lelewel4/Vest-Indicator-bachelor-thesis/Code/Steering wheel - TX/Core/Inc/ADC_functions.h

/*
 * ADC_functions.h
 *
 *  Created on: 12 gru 2022
 *      Author: Jakub Górnisiewicz
 */

#ifndef INC_OTHER_FUNCTIONS_H_
#define INC_OTHER_FUNCTIONS_H_


/*/////////////////////////////////////////////////////////////////////////////
 	 	 	 	 	 	 	 	 DEFINE
*//////////////////////////////////////////////////////////////////////////////

#define DEBUG_PRINTF
//define of the time of high-state diodes to show battery voltage
#define DIODES_ADC_TIME 500


/*/////////////////////////////////////////////////////////////////////////////
 	 	 	 	 	 	 	 	 INCLUDES
*//////////////////////////////////////////////////////////////////////////////


#include "main.h"


/*/////////////////////////////////////////////////////////////////////////////
 	 	 	 	 	 	 	 	 VARIABLES
*//////////////////////////////////////////////////////////////////////////////


//variable for ADC, measurement of battery voltage
extern uint32_t adc_value;


/*/////////////////////////////////////////////////////////////////////////////
 	 	 	 	 	 	 	 	 FUNCTIONS
*//////////////////////////////////////////////////////////////////////////////

uint32_t get_adc_battery_value(void);
void battery_level_show(uint32_t value);


#endif /* INC_OTHER_FUNCTIONS_H_ */
