lelewel4/Vest-Indicator-bachelor-thesis/Code/Steering wheel - TX/Core/Inc/nRF24.h

/*
 * nRF24.h
 *
 *  Created on: 16 paź 2022
 *      Author: Jakub Górnisiewicz
 */

#ifndef INC_NRF24_NRF24_H_
#define INC_NRF24_NRF24_H_


/*/////////////////////////////////////////////////////////////////////////////
 	 	 	 	 	 	 	 	 INCLUDES
*//////////////////////////////////////////////////////////////////////////////


#include "main.h"


/*/////////////////////////////////////////////////////////////////////////////
 	 	 	 	 	 	 	 	 VARIABLES
*//////////////////////////////////////////////////////////////////////////////


extern volatile uint8_t nrf24_rx_flag, nrf24_tx_flag, nrf24_mr_flag;


/*/////////////////////////////////////////////////////////////////////////////
 	 	 	 	 	 	 	 	 FUNCTIONS
*//////////////////////////////////////////////////////////////////////////////


void nRF24_Init(SPI_HandleTypeDef *hspi);


// READ/WRITE REGISTERS
uint8_t nRF24_ReadConfig(void);
void nRF24_WriteConfig(uint8_t conf);
uint8_t nRF24_ReadStatus();
void nRF24_WriteStatus(uint8_t st);

// SWITCHING BETWEEN RX AND TX
void nRF24_RX_Mode(void);
void nRF24_TX_Mode(void);

// RADIO SETTINGS
void nRF24_SetPALevel(uint8_t lev);
void nRF24_SetDataRate(uint8_t dr);
void nRF24_EnableCRC(uint8_t onoff);
void nRF24_SetCRCLength(uint8_t crcl);
void nRF24_SetRetries(uint8_t ard, uint8_t arc);
void nRF24_SetRFChannel(uint8_t channel);
void nRF24_SetPayloadSize(uint8_t pipe, uint8_t size);
void nRF24_EnablePipe(uint8_t pipe, uint8_t onoff);
void nRF24_AutoACK(uint8_t pipe, uint8_t onoff);
void nRF24_SetRXAddress(uint8_t pipe, uint8_t* address); // Remember to define RX address before TX
void nRF24_SetTXAddress(uint8_t* address);
void nRF24_SetAddressWidth(uint8_t size);

// INTERRUPT CONTROL
void nRF24_ClearInterrupts(void);
void nRF24_EnableRXDataReadyIRQ(uint8_t onoff);
void nRF24_EnableTXDataSentIRQ(uint8_t onoff);
void nRF24_EnableMaxRetransmitIRQ(uint8_t onoff);

// PUSH/PULL DATA TO PAYLOAD
void nRF24_WriteTXPayload(uint8_t* data);
void nRF24_WaitTX();
void nRF24_ReadRXPaylaod(uint8_t* data);

// TRANSMITTING DATA
void nRF24_SendPacket(uint8_t* data);
void nRF24_ReceivePacket(uint8_t* data);

// FLUSHING FIFOs
void nRF24_FlushRX(void);
void nRF24_FlushTX(void);


// IRQ HANDLER
void nRF24_IRQ_Handler(void);

// POLLING METHOD
uint8_t nRF24_RXAvailible(void);

#endif /* INC_NRF24_NRF24_H_ */
